snoopy3921/Leta/assets/case.gif

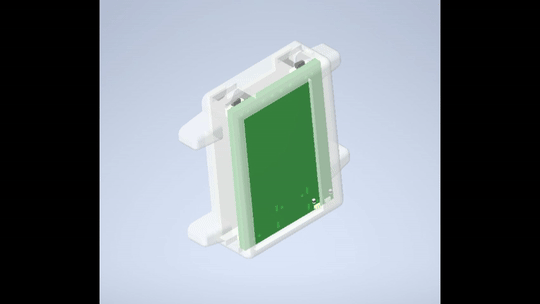
assets/case.gif
