snoopy3921/Leta/assets/Schema.png

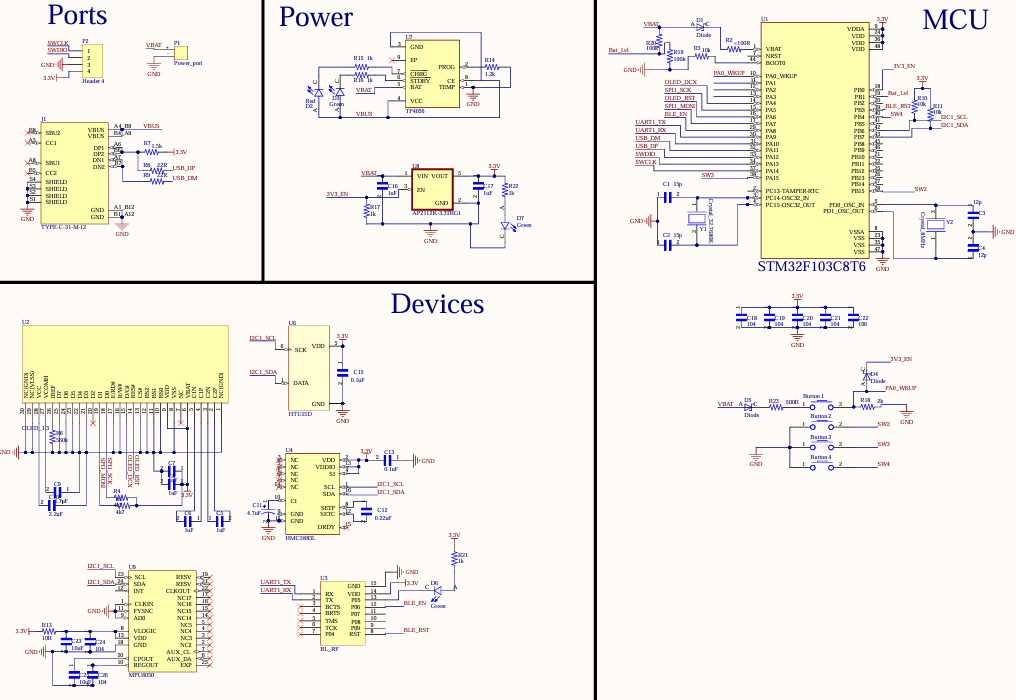
assets/Schema.png
